ijnekenamay/picotracker_alt-pcb/images/3.png

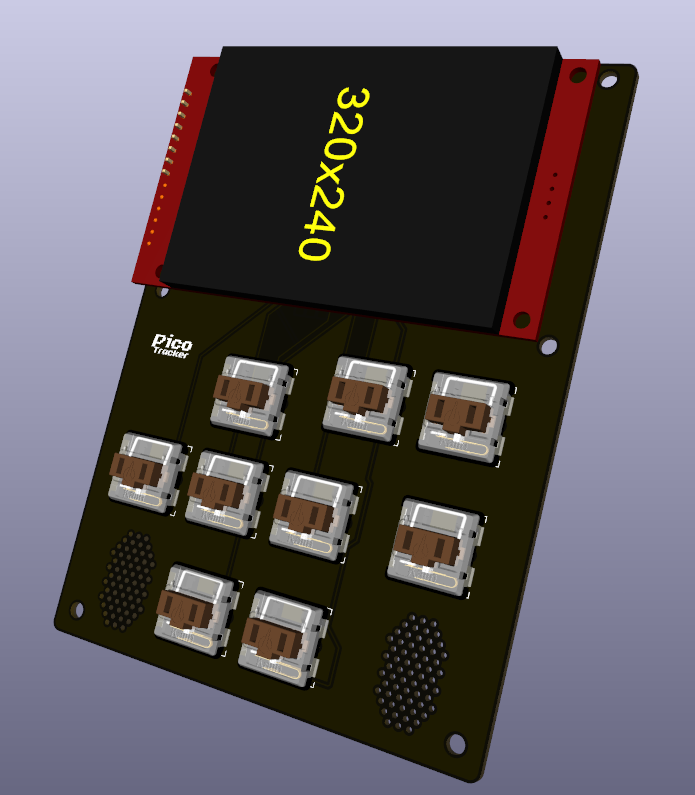
images/3.png
