ijnekenamay/picotracker_alt-pcb/images/4.png

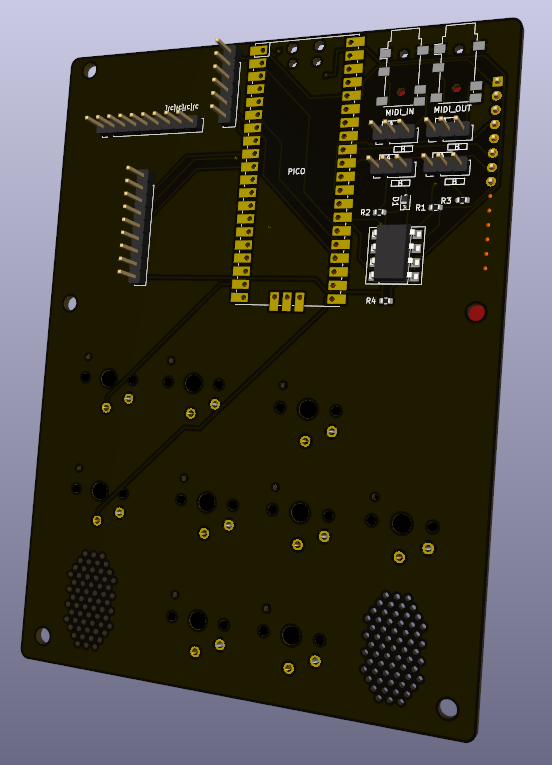
images/4.png
