ijnekenamay/picotracker_alt-pcb/images/5.png

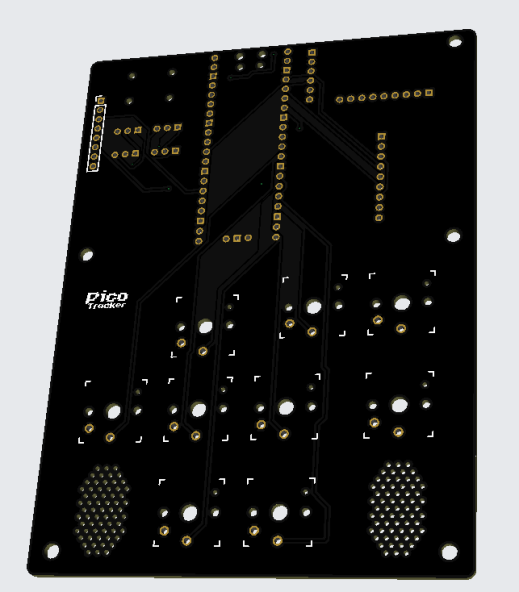
images/5.png
