ijnekenamay/picotracker_alt-pcb/images/6.png

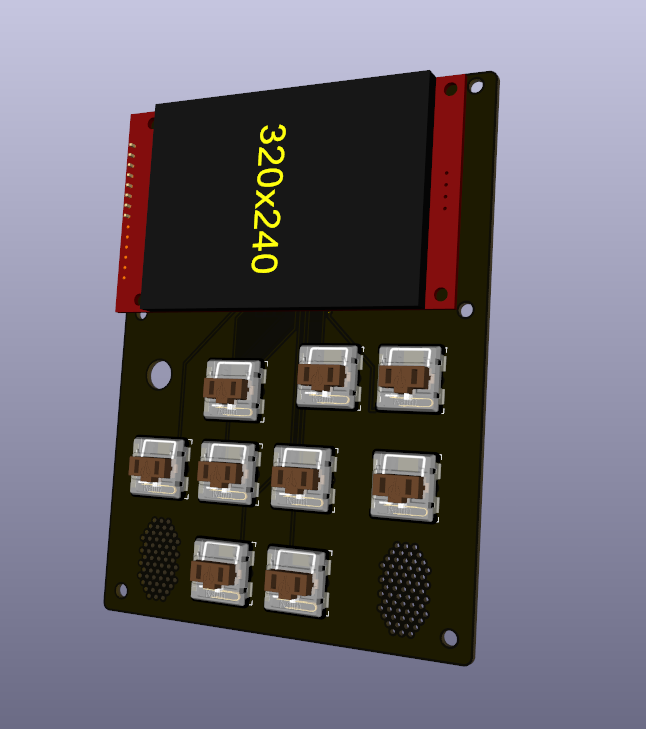
images/6.png
