ijnekenamay/picotracker_alt-pcb/images/7.png

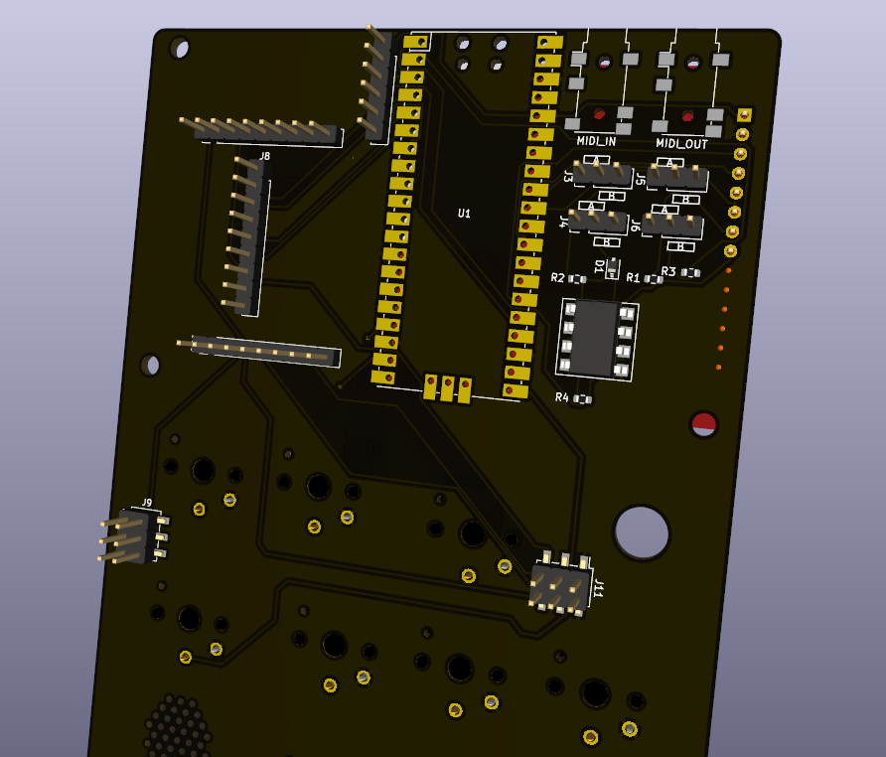
images/7.png
