ijnekenamay/picotracker_alt-pcb/kicad/adafruit_products_MIDI_FW_sch.png

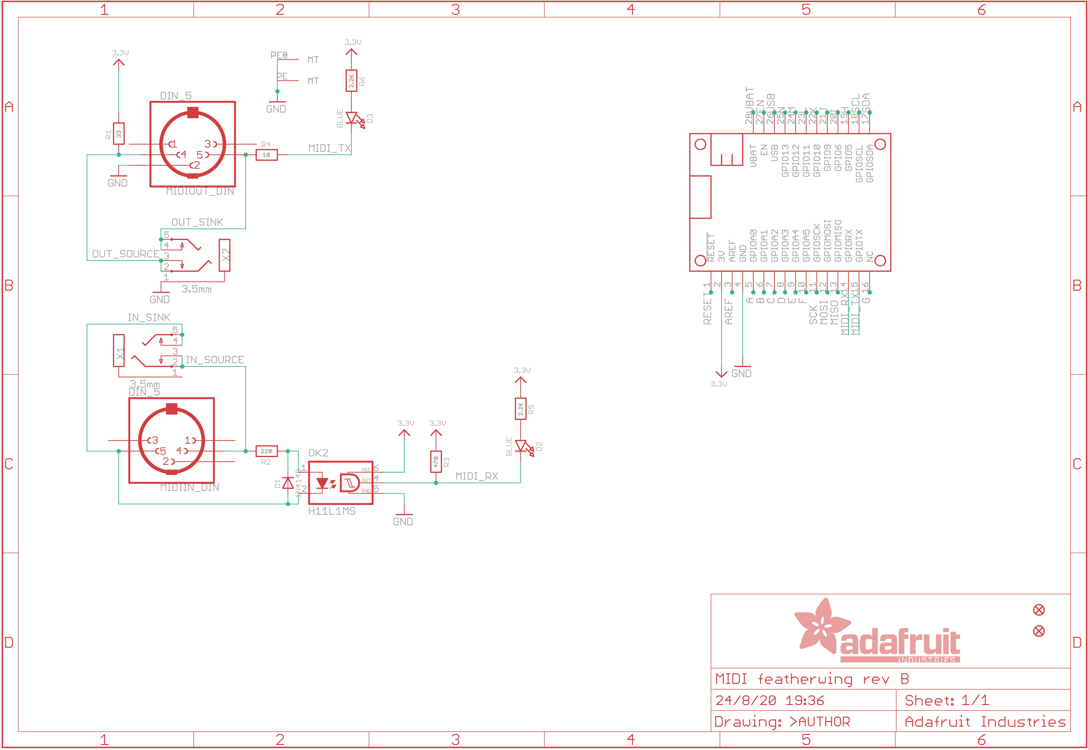
kicad/adafruit_products_MIDI_FW_sch.png
